mohdsaad7281/Buck-convertor-simulation/buckconvertor.asc

C1: cap; 5µ
D1: diode
L1: ind; 146µ; Rser=1m
R1: res; 5
S1: sw; SW1
V1: voltage; 12
V2: voltage; PULSE(0 5 0 10n 10n 4.17u 10u)
Named nets: 0
.model SW1 SW(Ron=0.01 Roff=1Meg Vt=2.5 Vh=0.1)
.tran 2m
.meas TRAN Vout_avg AVG V(n005) FROM 1.5m TO 2m
.meas TRAN IL_avg AVG I(L1) FROM 1.5m TO 2m
.meas TRAN Pin_avg AVG (V(N001)*I(V1)) FROM 1.5m TO 2m
.meas TRAN Pout_avg AVG (V(n005)*V(n005)/5) FROM 1.5m TO 2m
